NarrowJS/SolarPlanter/Assets/photo-2.png

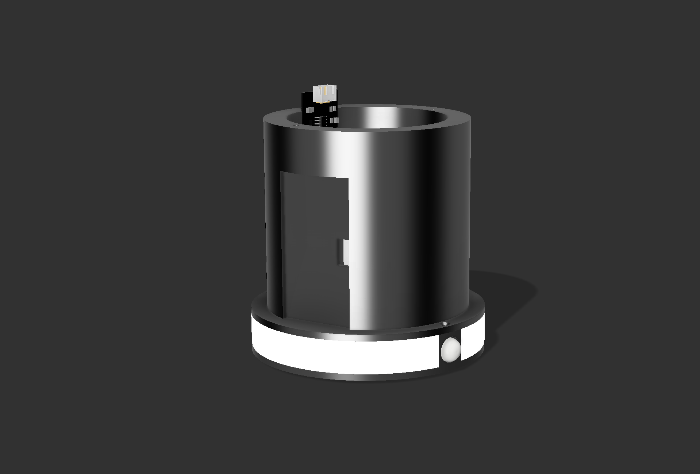
Assets/photo-2.png
